akkdong/PowerCube/hw/schematic/symbols/20630846.png

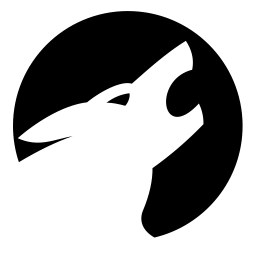
hw/schematic/symbols/20630846.png
